VirtualConcrete/LEDPanelsControl/Software/nano_v3/rotating_text/rotating_text.ino

/*
  Scrolling alphabet demo, displays characters one at a time into a scrolling box.
 */

#include <SPI.h>
#include <DMD2.h>
#include <fonts/SystemFont5x7.h>
#include <fonts/Arial_Black_16.h>
#include <fonts/Arial14.h>

// Set Width to the number of displays wide you have
const int WIDTH = 2;

// You can change to a smaller font (two lines) by commenting this line,
// and uncommenting the line after it:
const uint8_t *FONT = Arial_Black_16;
//const uint8_t *FONT = Arial14;
//const uint8_t *FONT = SystemFont5x7;

const String message = " SOPPA ";

SoftDMD dmd(WIDTH, 1);  // DMD controls the entire display
DMD_TextBox box(dmd, 0, 0, 32, 16);  // "box" provides a text box to automatically write to/scroll the display

// the setup routine runs once when you press reset:
void setup() {
  Serial.begin(9600);
  dmd.setBrightness(255);
  dmd.selectFont(FONT);
  dmd.begin();
  dmd.drawString(0, 0, message);
}

int phase = -1;

// the loop routine runs over and over again forever:
void loop() {
  switch(phase) {
    case 0:
      dmd.marqueeScrollX(1); break;
    case 1:
      dmd.marqueeScrollX(-1); break;
    case 2:
      dmd.marqueeScrollY(1); break;
    case 3:
      dmd.marqueeScrollY(-1); break;
  }
  delay(100);
/*  const char *next = MESSAGE;
  while(*next) {
    Serial.print(*next);
    box.print(*next);
    delay(200);
    next++;
  }
*/
}
